MeIsGaggy/MTG-Card-Scanner-Sorter/AI Model Data/Results/confusion_matrix.png

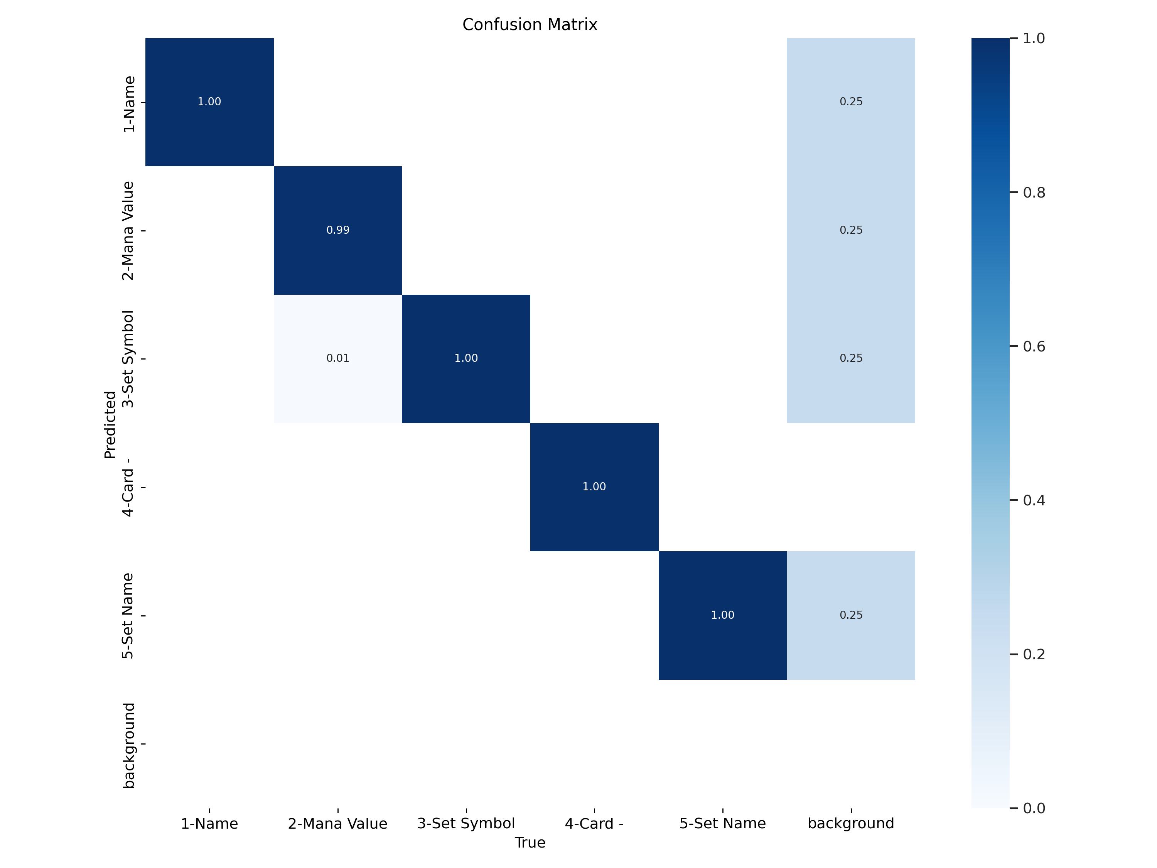
AI Model Data/Results/confusion_matrix.png
