MeIsGaggy/MTG-Card-Scanner-Sorter/AI Model Data/Results/F1_curve.png

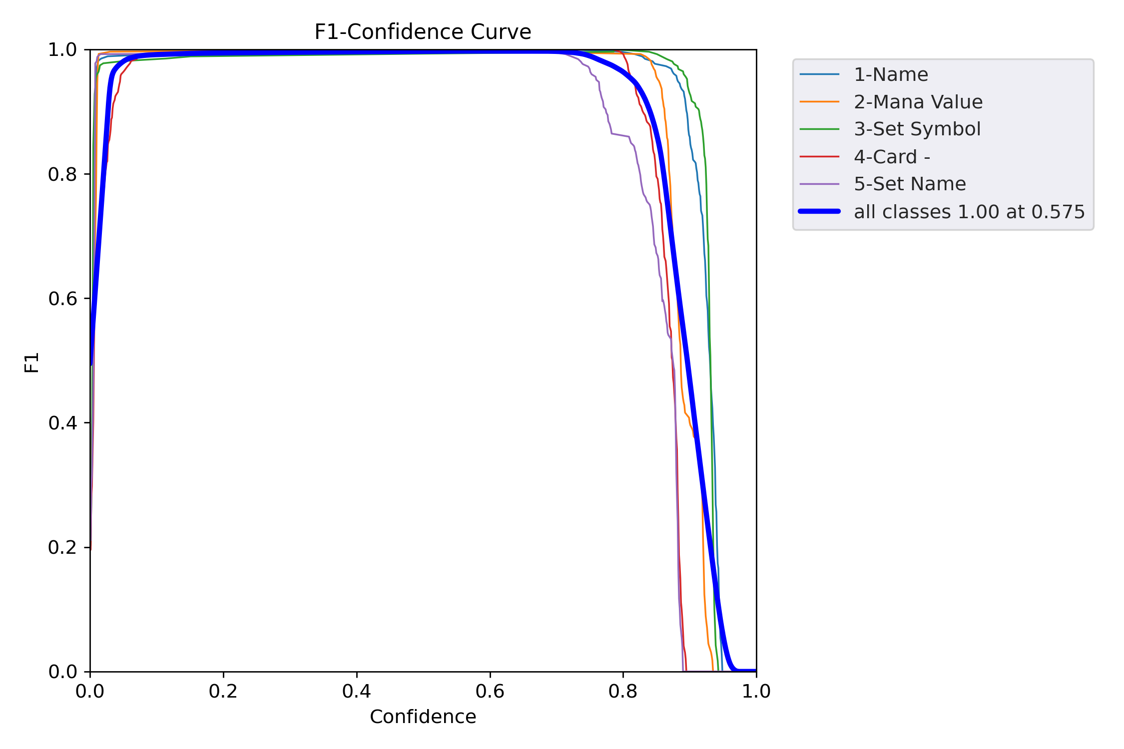
AI Model Data/Results/F1_curve.png
