MeIsGaggy/MTG-Card-Scanner-Sorter/AI Model Data/Results/labels.jpg

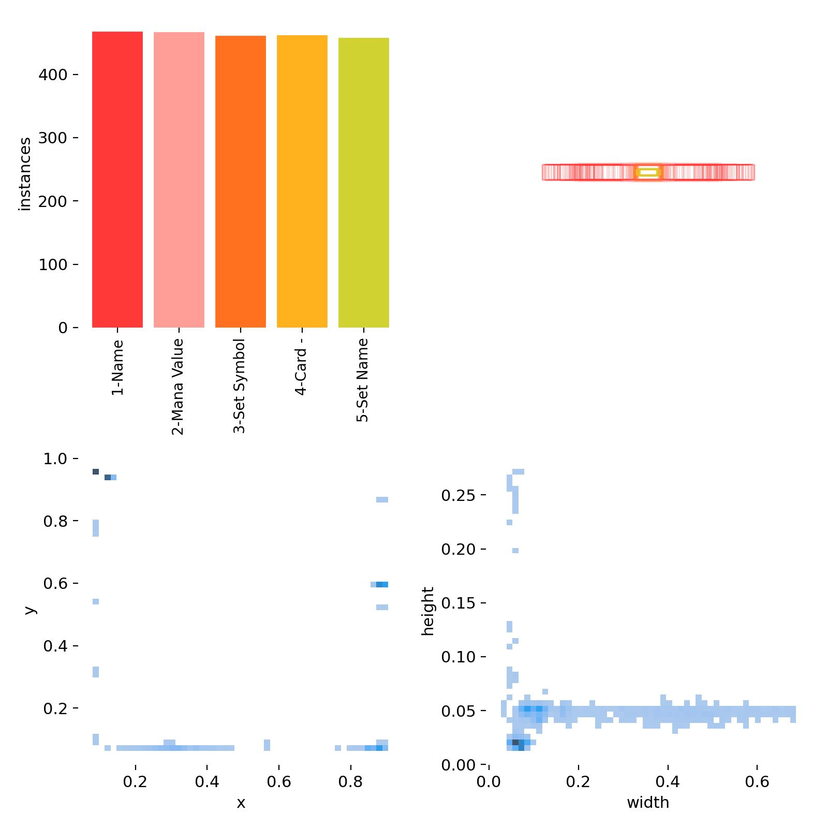
AI Model Data/Results/labels.jpg
