MeIsGaggy/MTG-Card-Scanner-Sorter/AI Model Data/Results/labels_correlogram.jpg

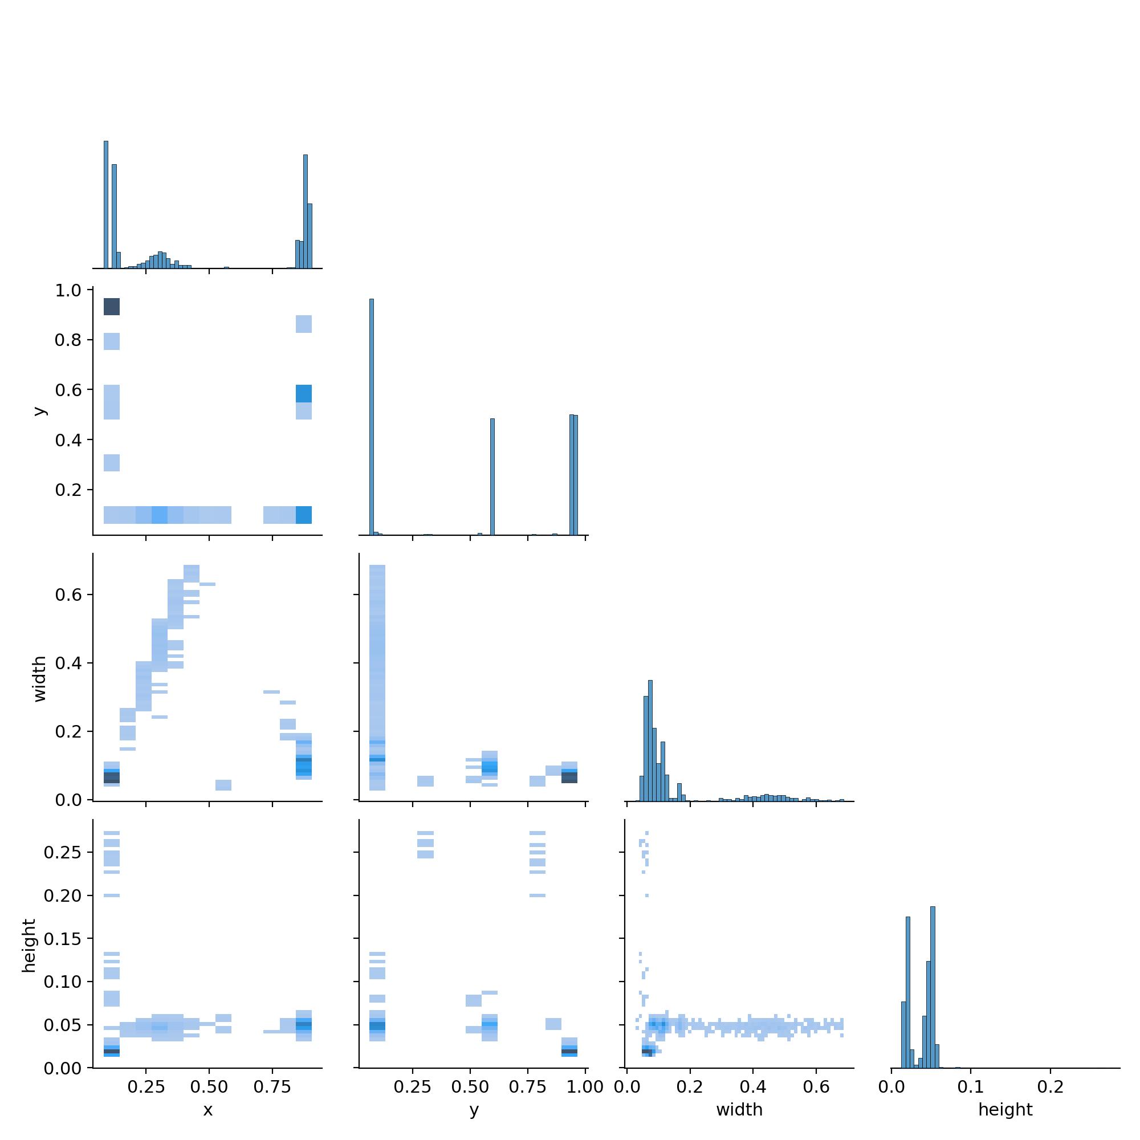
AI Model Data/Results/labels_correlogram.jpg
