MeIsGaggy/MTG-Card-Scanner-Sorter/AI Model Data/Results/P_curve.png

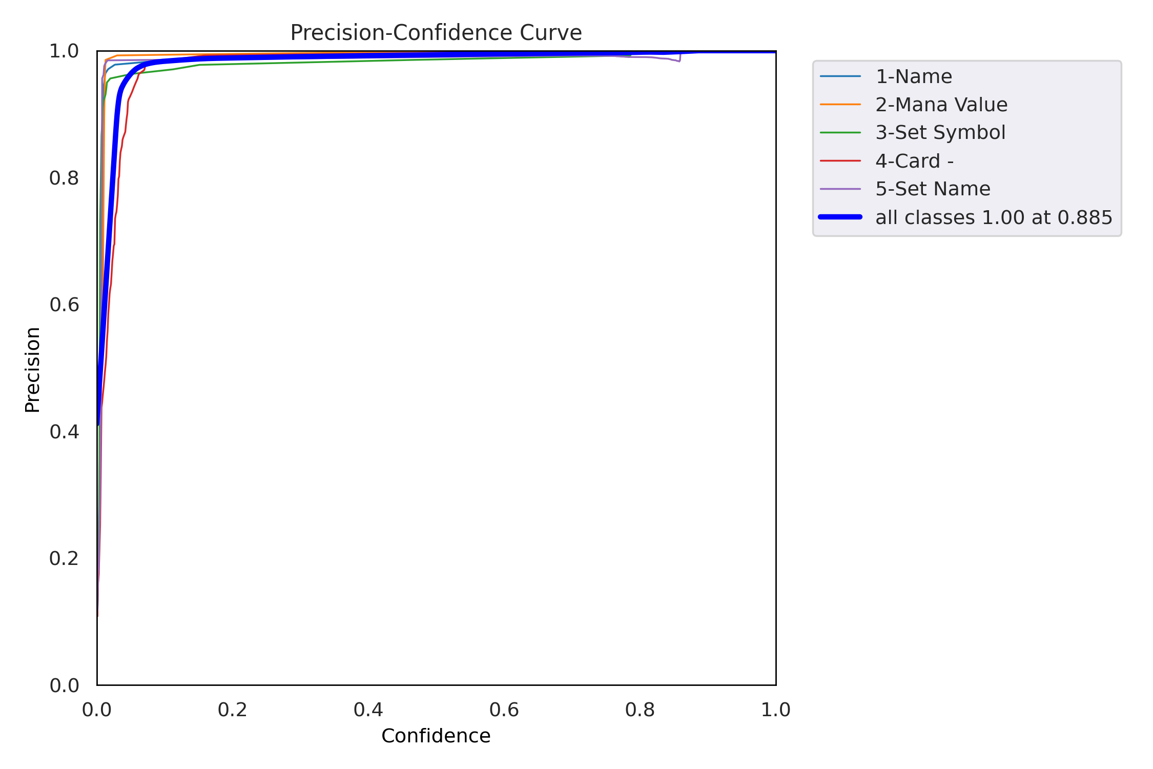
AI Model Data/Results/P_curve.png
