MeIsGaggy/MTG-Card-Scanner-Sorter/AI Model Data/Results/PR_curve.png

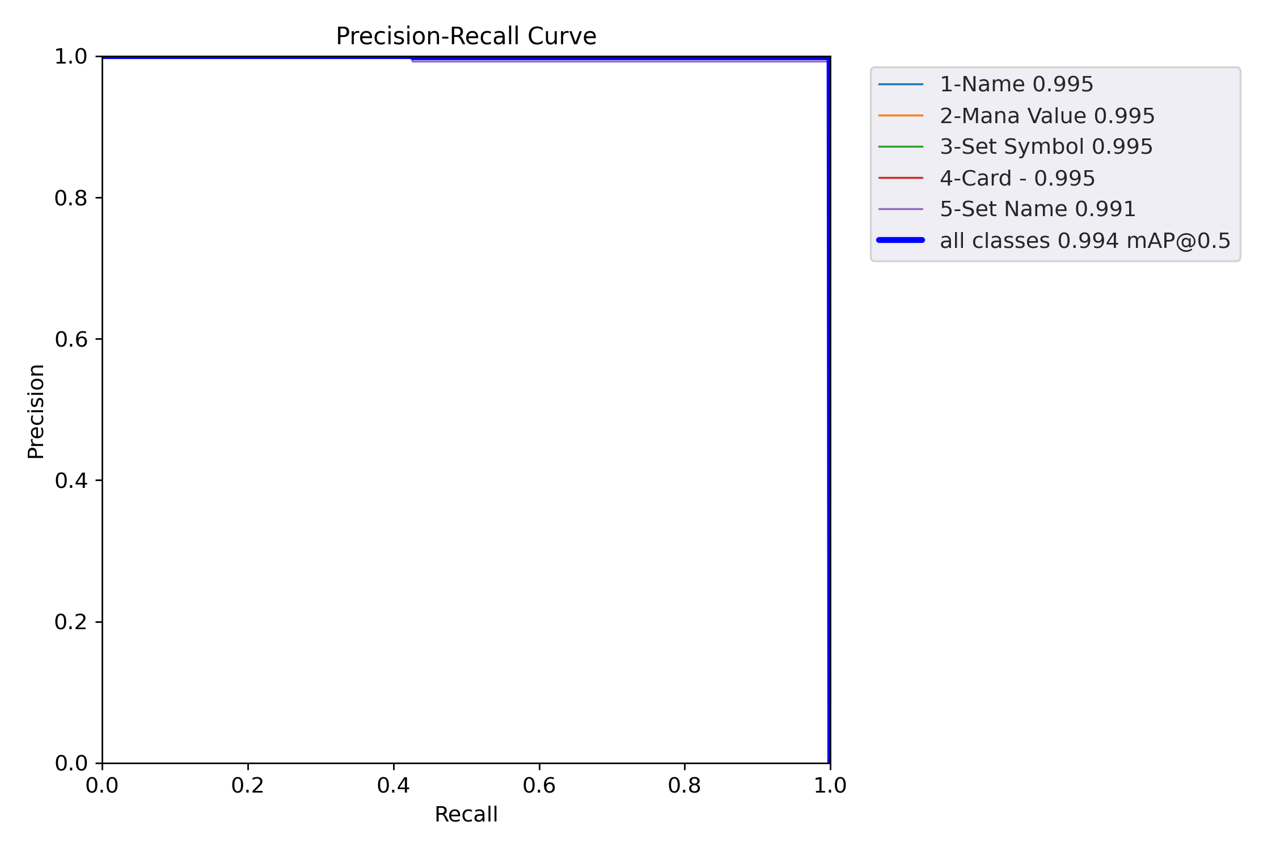
AI Model Data/Results/PR_curve.png
