MeIsGaggy/MTG-Card-Scanner-Sorter/AI Model Data/Results/results.png

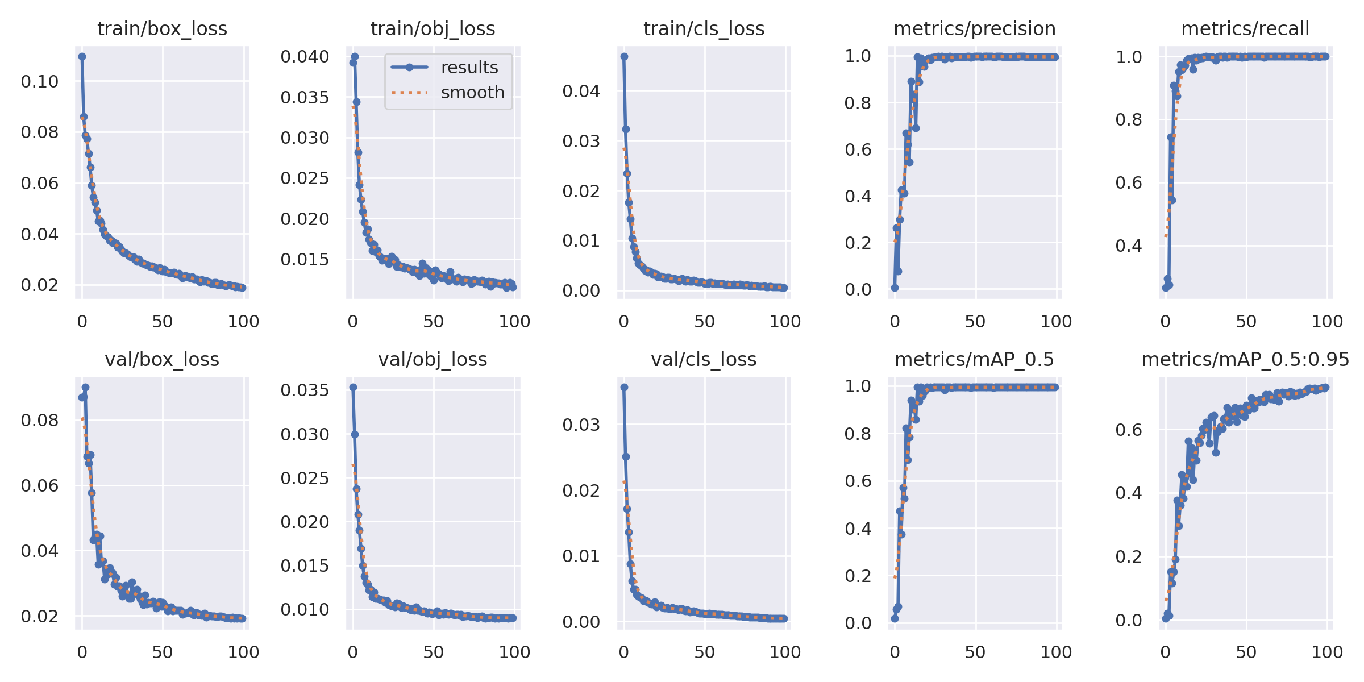
AI Model Data/Results/results.png
