MeIsGaggy/MTG-Card-Scanner-Sorter/AI Model Data/Results/train_batch0.jpg

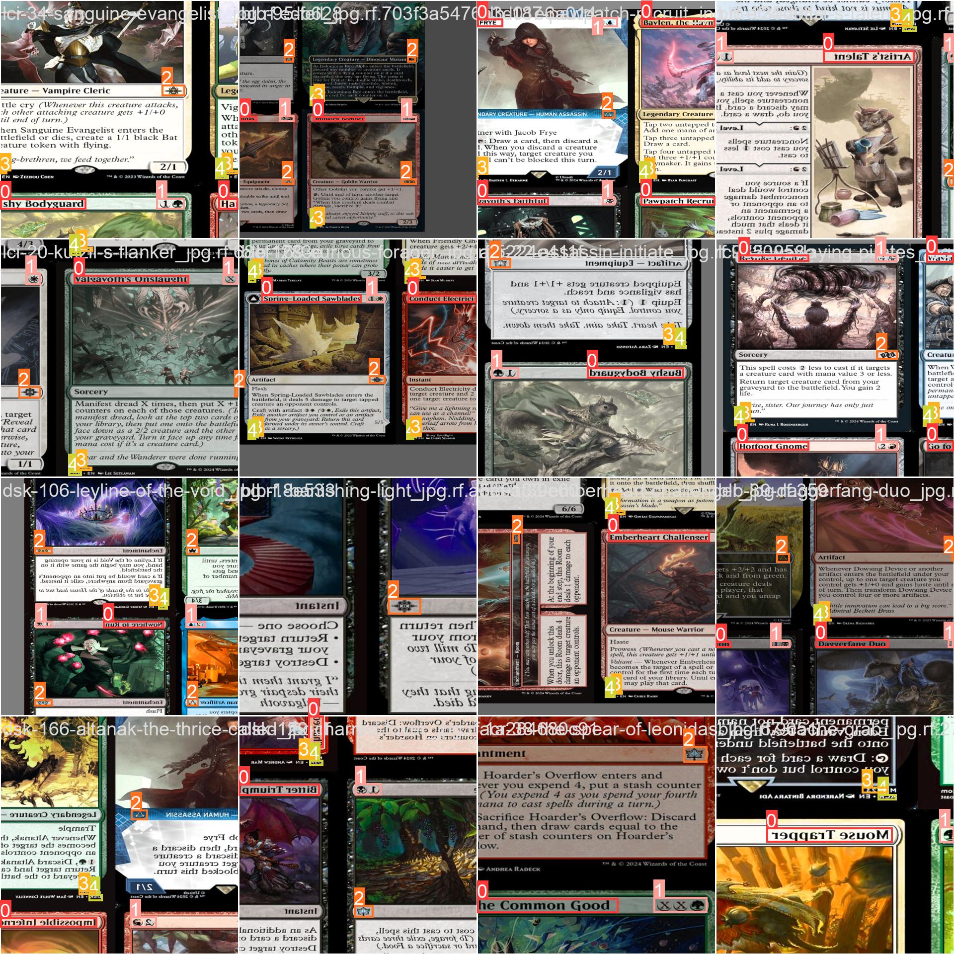
AI Model Data/Results/train_batch0.jpg
