MeIsGaggy/MTG-Card-Scanner-Sorter/AI Model Data/Results/train_batch1.jpg

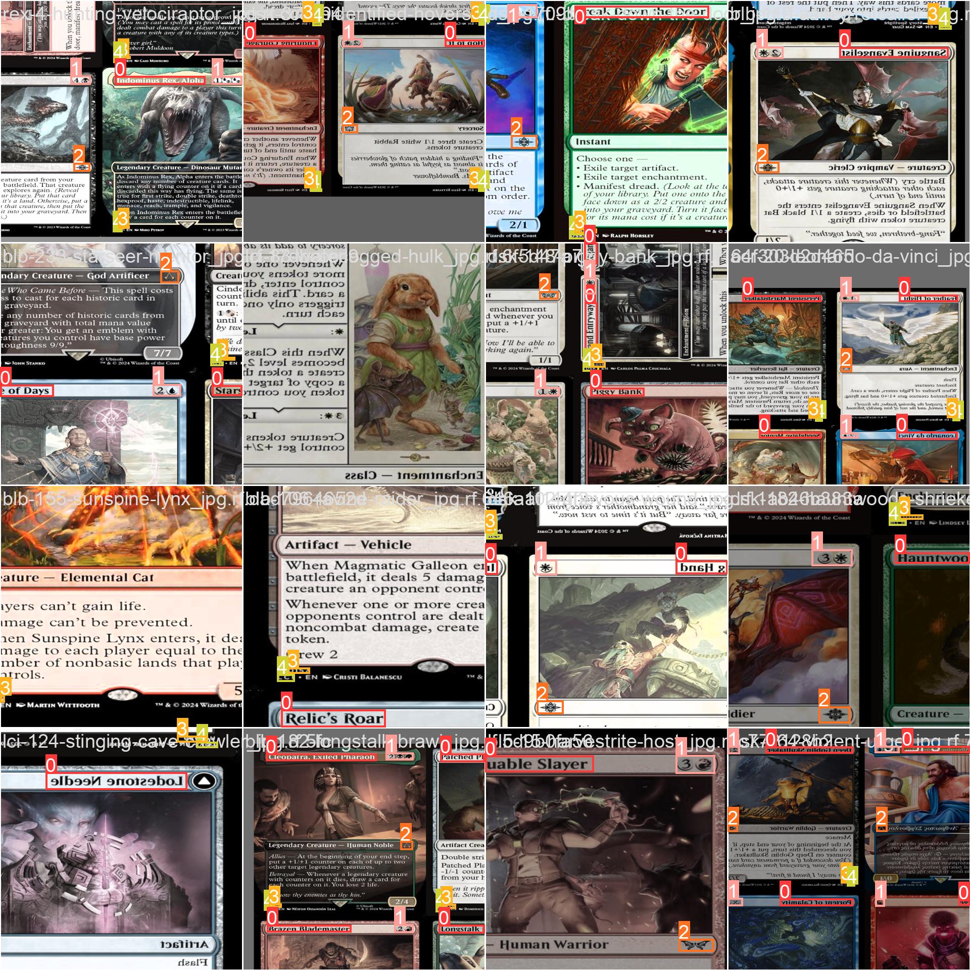
AI Model Data/Results/train_batch1.jpg
