MeIsGaggy/MTG-Card-Scanner-Sorter/AI Model Data/Results/train_batch2.jpg

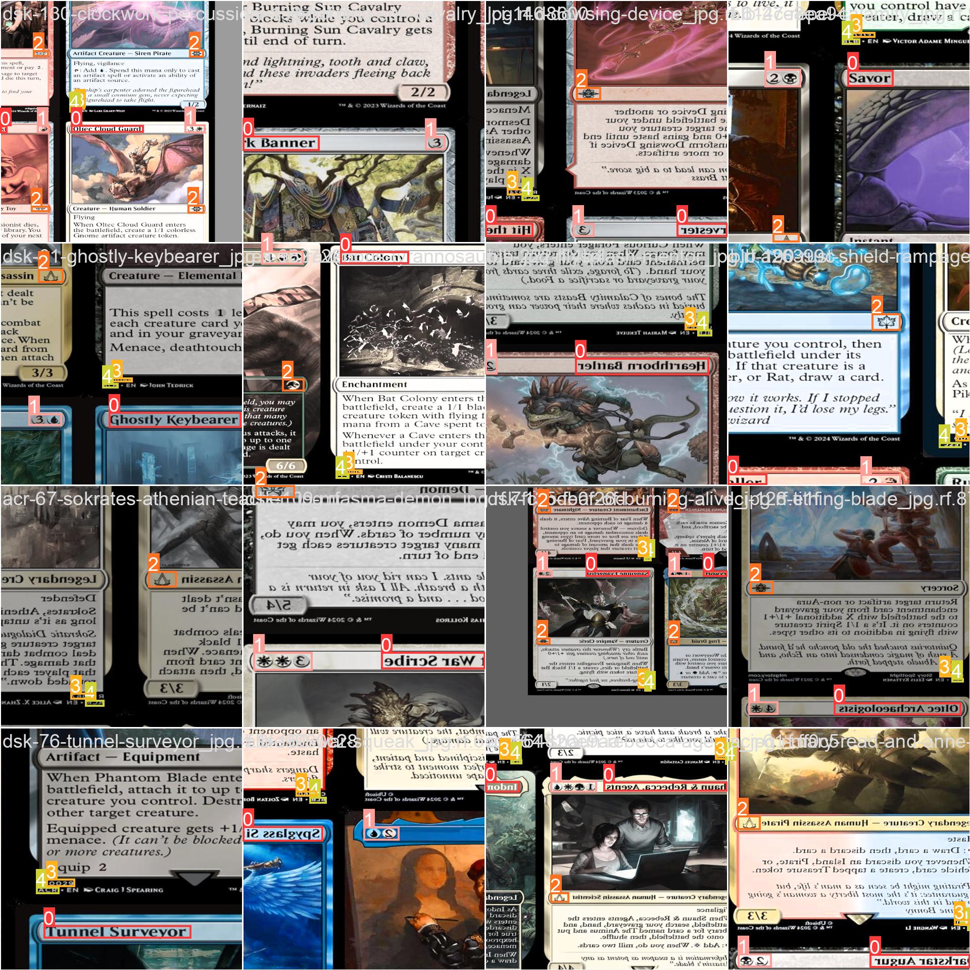
AI Model Data/Results/train_batch2.jpg
