MeIsGaggy/MTG-Card-Scanner-Sorter/AI Model Data/Results/val_batch0_labels.jpg

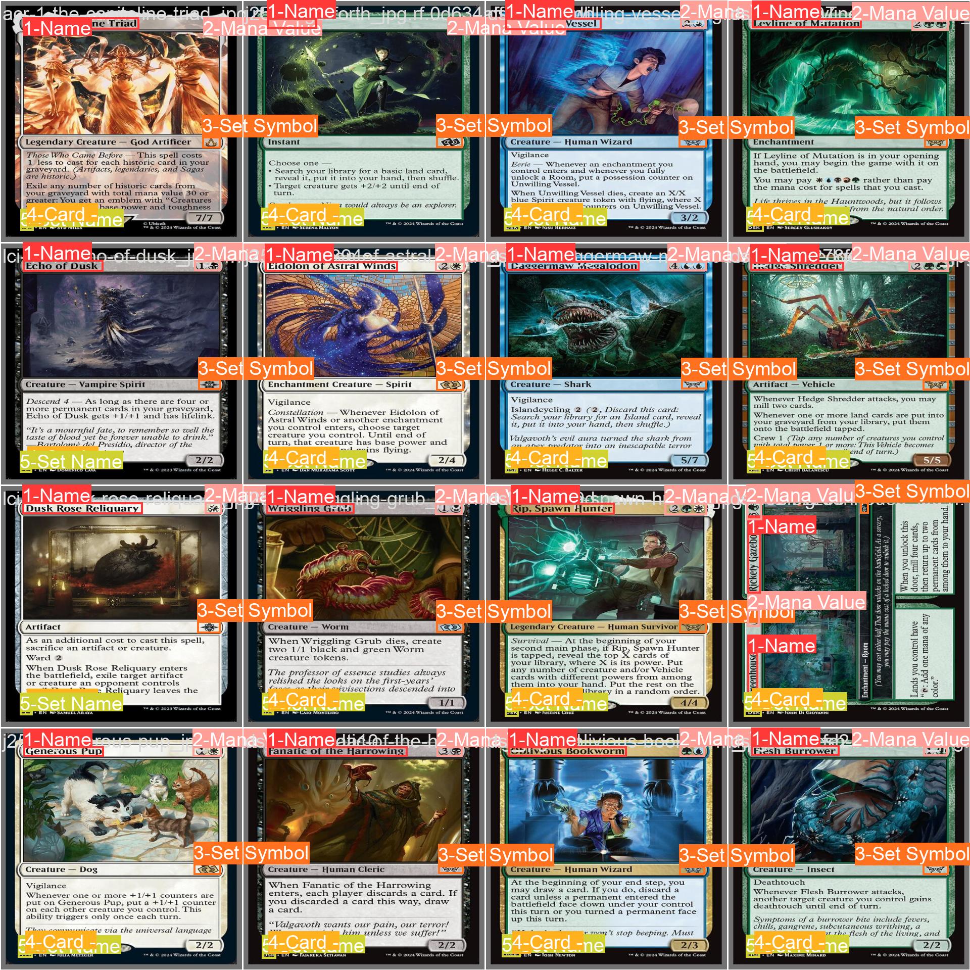
AI Model Data/Results/val_batch0_labels.jpg
