MeIsGaggy/MTG-Card-Scanner-Sorter/AI Model Data/Results/val_batch1_labels.jpg

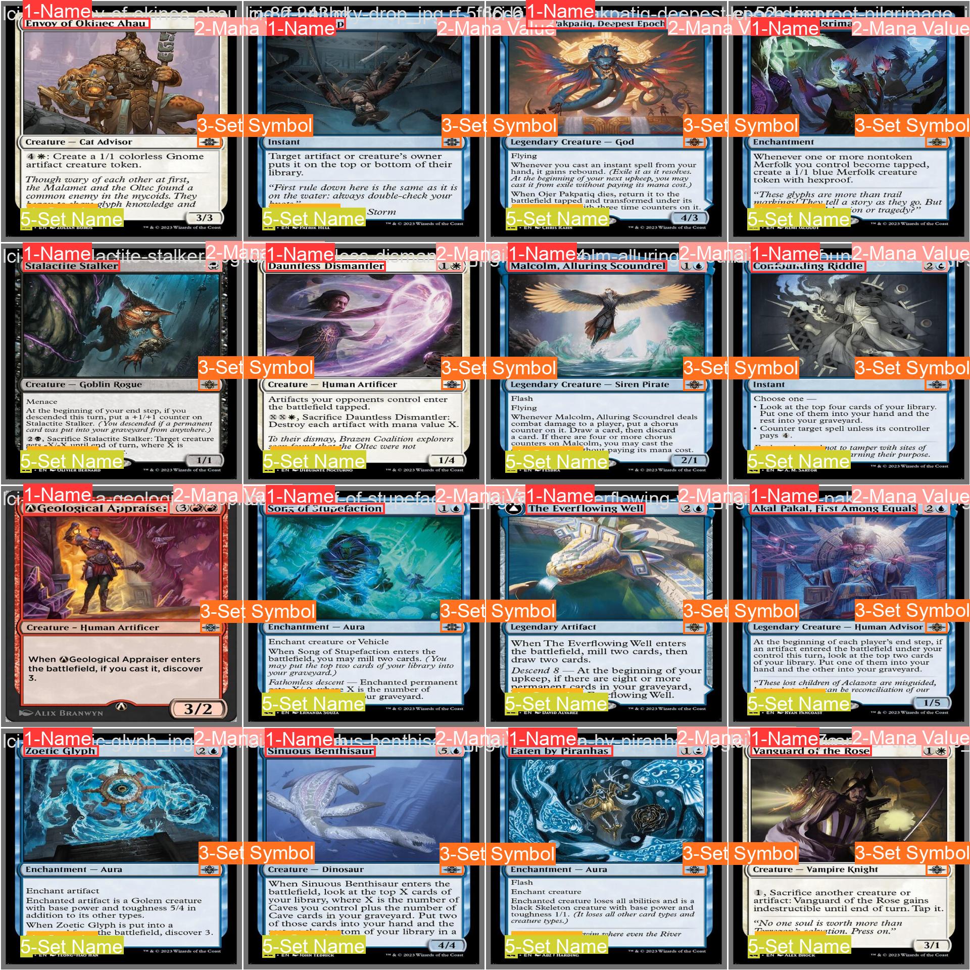
AI Model Data/Results/val_batch1_labels.jpg
