MeIsGaggy/MTG-Card-Scanner-Sorter/AI Model Data/Results/val_batch2_labels.jpg

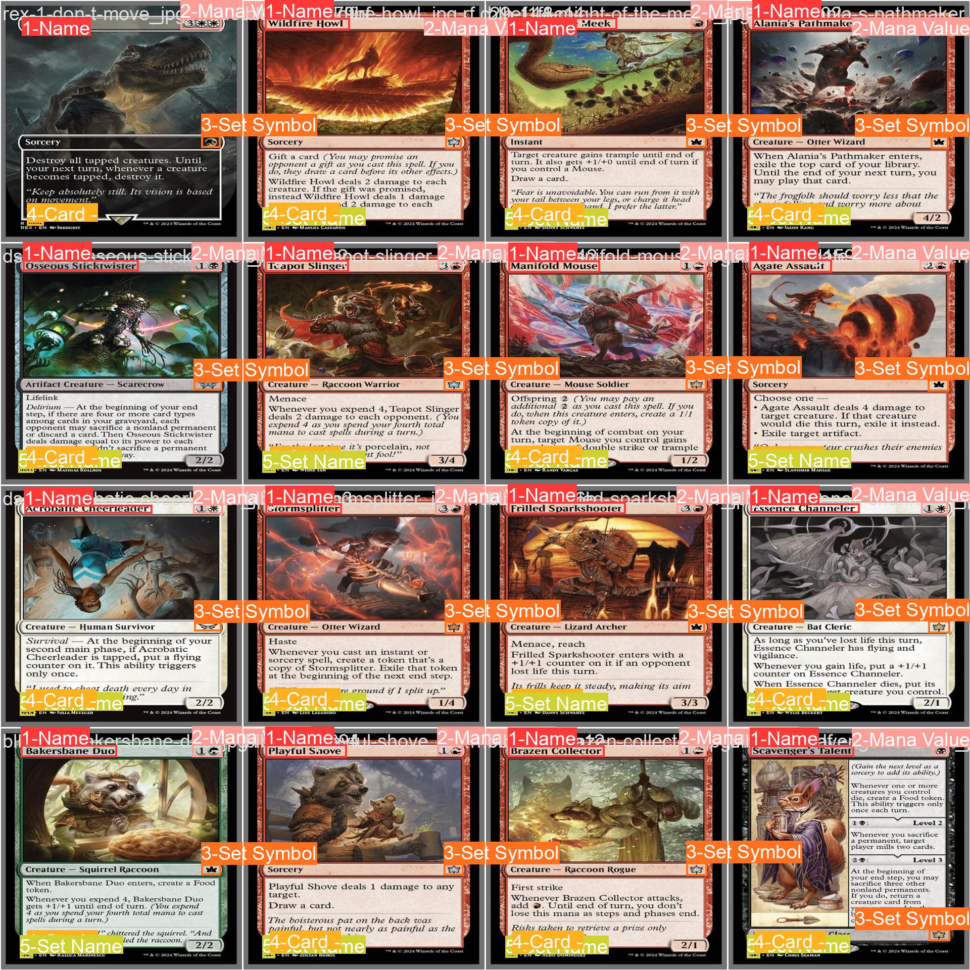
AI Model Data/Results/val_batch2_labels.jpg
